weteor/Fitis/pcb/fitis.kicad_sch

## KiCad design pcb/fitis.kicad_sch (2024-07-09)

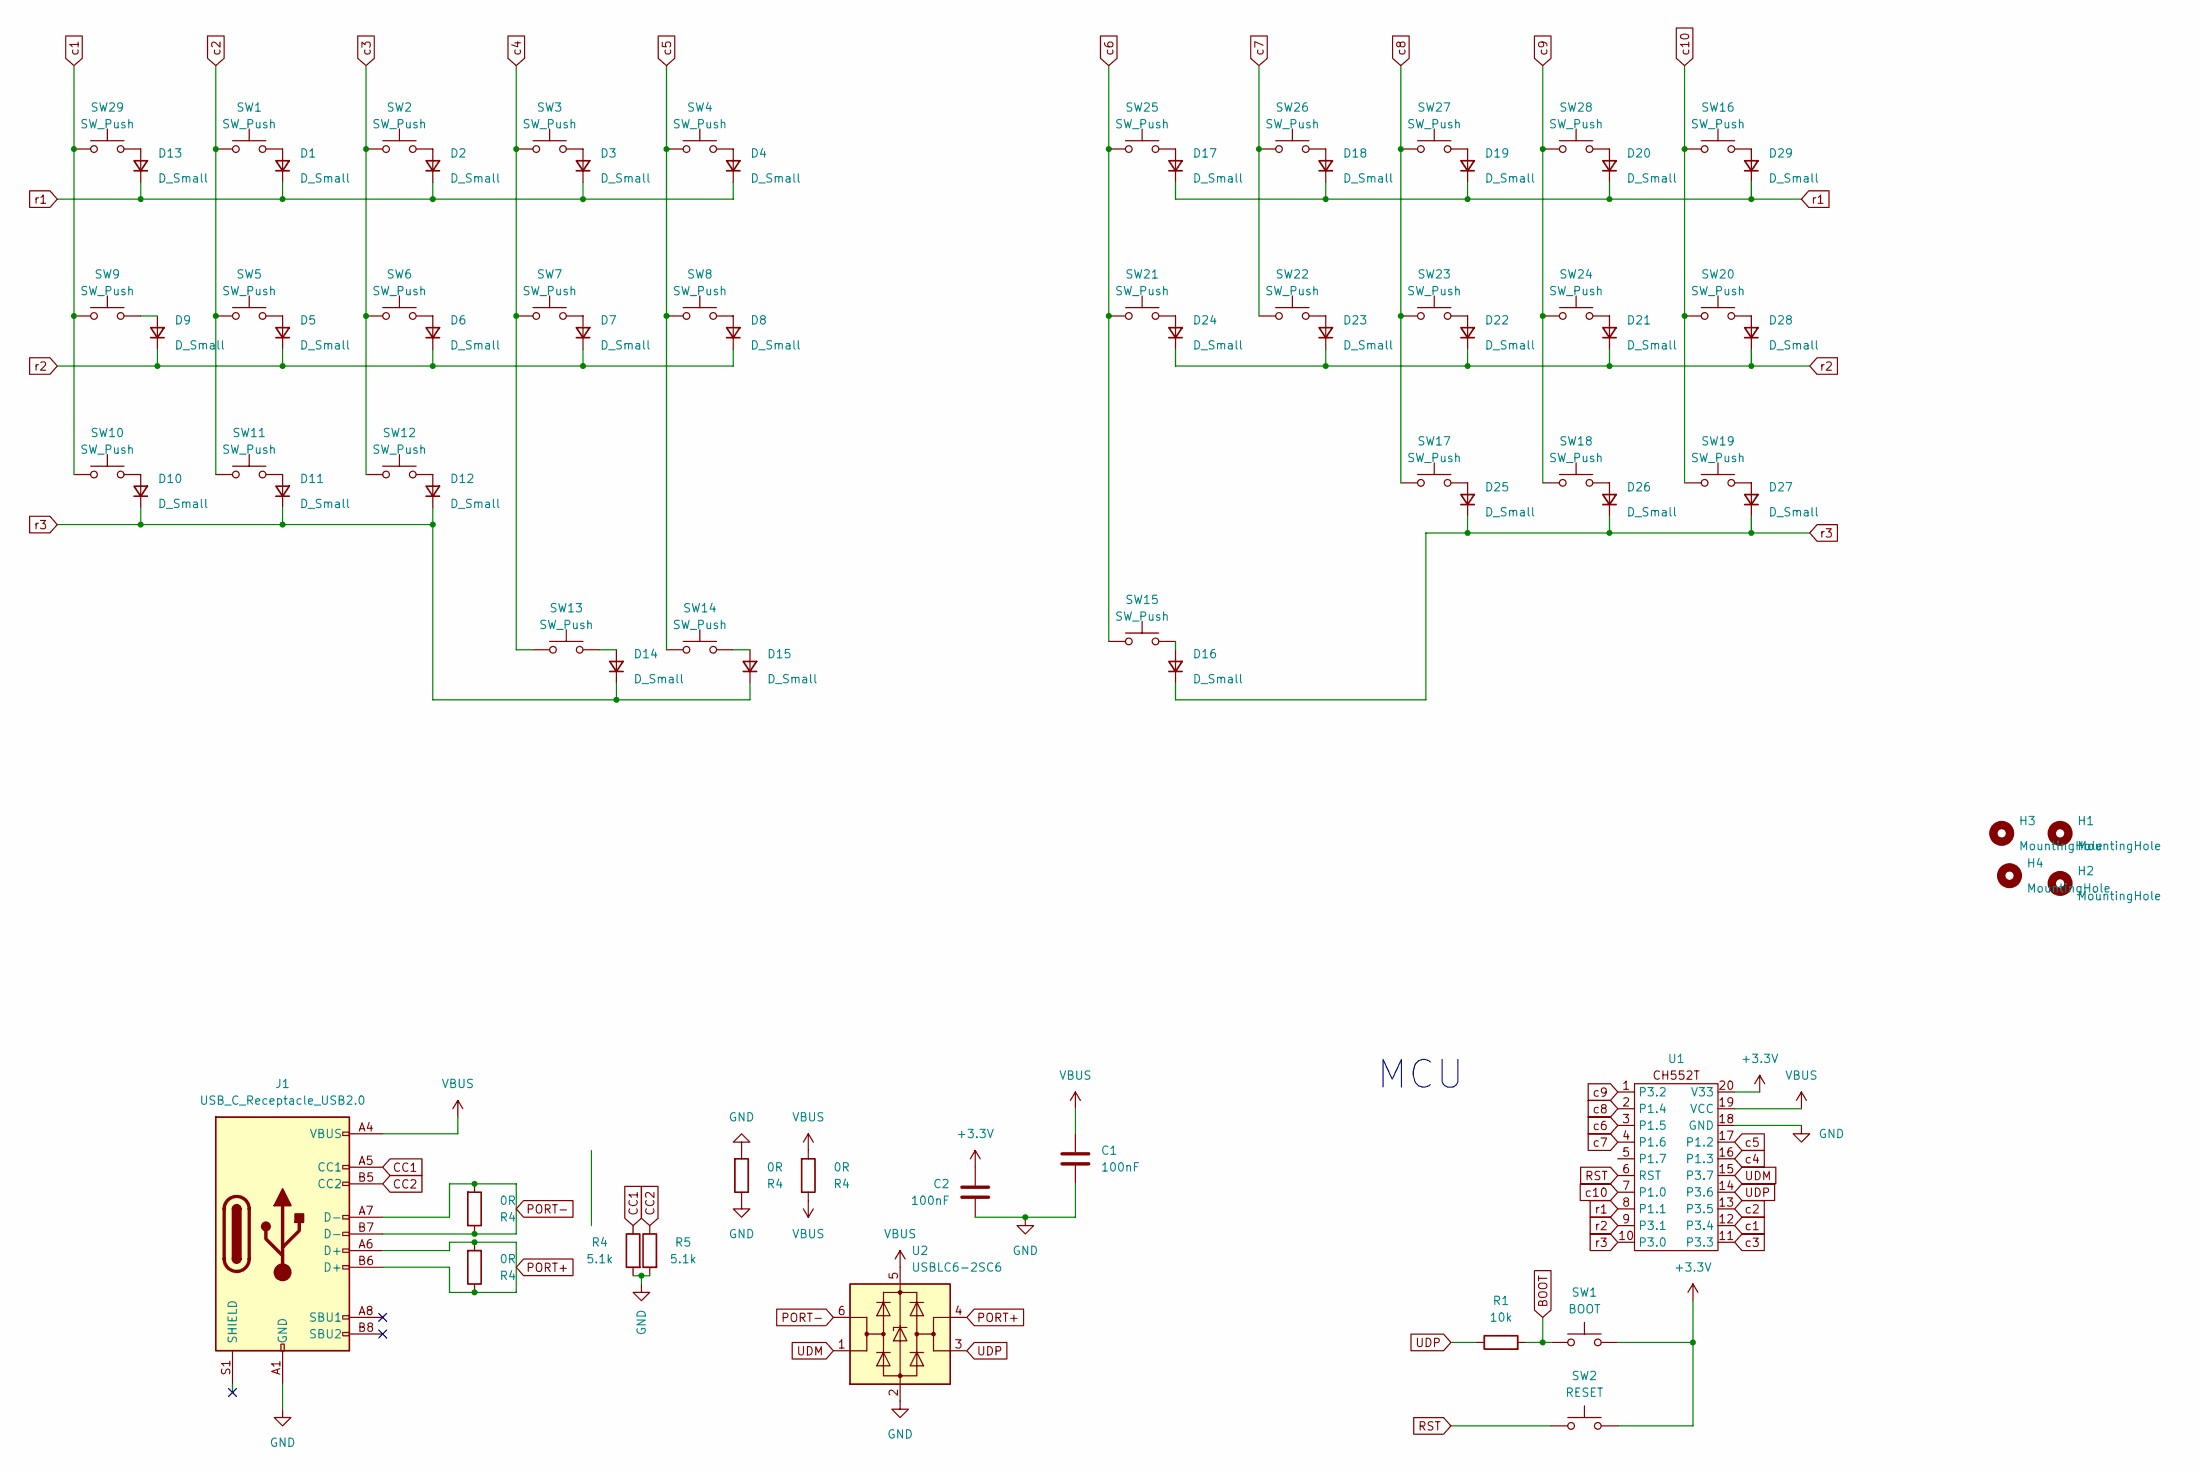
[picture p4: schematic fitis.kicad_sch]

Parts:
C1, C2: 100nF; C_0603_HandSolder; LCSC C1525
D1, D2, D3, D4, D5, D6, D7, D8, D9, D10, D11, D12, D13, D14, D15, D16, D17, D18, D19, D20, D21, D22, D23, D24, D25, D26, D27, D28, D29: D_Small; D_SOD-123
H1, H2, H3, H4: MountingHole; MountingHole_2.2mm_M2
J1: USB_C_Receptacle_USB2.0; USB-C-12-Pin-MidMount
R1: 10k; R_0603_HandSolder; LCSC C25744
R4: 0R; R_0603_HandSolder
R5: 5.1k; R_0603_HandSolder
SW1: BOOT; SW_SPST_TL3342; LCSC C115357
SW2: RESET; SW_SPST_TL3342; LCSC C115357
SW3, SW4, SW5, SW6, SW7, SW8, SW9, SW10, SW11, SW12, SW13, SW14, SW16, SW17, SW18, SW19, SW20, SW21, SW22, SW23, SW24, SW25, SW26, SW27, SW28, SW29: SW_Push; ChocV1_V2_Hotswap_3d
SW15: SW_Push; ChocV1_V2_Hotswap_1.5u_3d
U1: TSSOP-20_4.4x6.5mm_P0.65mm; JLCPCB_CORRECTION 0; 0; 270
U2: USBLC6-2SC6; SOT-23-6; JLCPCB_CORRECTION 0; 0; 270

Connections:
+3.3V: C2.1, SW1.2, SW2.2, U1.20 (V33)
BOOT: R1.2, SW1.1
CC1: J1.A5 (CC1), R4.1
CC2: J1.B5 (CC2), R5.1
GND: C1.2, C2.2, J1.A1 (GND), J1.A12 (GND), J1.B1 (GND), J1.B12 (GND), R4.1, R4.2, R5.2, U1.18 (GND), U2.2 (GND)
unnamed: D1.2 (A), SW1.2
unnamed: D2.2 (A), SW2.2
unnamed: D3.2 (A), SW3.2
unnamed: D4.2 (A), SW4.2
unnamed: D5.2 (A), SW5.2
unnamed: D6.2 (A), SW6.2
unnamed: D7.2 (A), SW7.2
unnamed: D8.2 (A), SW8.2
unnamed: D9.2 (A), SW9.2
unnamed: D10.2 (A), SW10.2
unnamed: D11.2 (A), SW11.2
unnamed: D12.2 (A), SW12.2
unnamed: D13.2 (A), SW29.2
unnamed: D14.2 (A), SW13.2
unnamed: D15.2 (A), SW14.2
unnamed: D16.2 (A), SW15.2
unnamed: D17.2 (A), SW25.2
unnamed: D18.2 (A), SW26.2
unnamed: D19.2 (A), SW27.2
unnamed: D20.2 (A), SW28.2
unnamed: D21.2 (A), SW24.2
unnamed: D22.2 (A), SW23.2
unnamed: D23.2 (A), SW22.2
unnamed: D24.2 (A), SW21.2
unnamed: D25.2 (A), SW17.2
unnamed: D26.2 (A), SW18.2
unnamed: D27.2 (A), SW19.2
unnamed: D28.2 (A), SW20.2
unnamed: D29.2 (A), SW16.2
PORT+: J1.A6 (D+), J1.B6 (D+), R4.1, R4.2, U2.4 (I/O2)
PORT-: J1.A7 (D-), J1.B7 (D-), R4.1, R4.2, U2.6 (I/O1)
RST: SW2.1, U1.6 (RST)
UDM: U1.15 (P3.7), U2.1 (I/O1)
UDP: R1.1, U1.14 (P3.6), U2.3 (I/O2)
VBUS: C1.1, J1.A4 (VBUS), J1.A9 (VBUS), J1.B4 (VBUS), J1.B9 (VBUS), R4.1, R4.2, U1.19 (VCC), U2.5 (VBUS)
c1: SW9.1, SW10.1, SW29.1, U1.12 (P3.4)
c2: SW1.1, SW5.1, SW11.1, U1.13 (P3.5)
c3: SW2.1, SW6.1, SW12.1, U1.11 (P3.3)
c4: SW3.1, SW7.1, SW13.1, U1.16 (P1.3)
c5: SW4.1, SW8.1, SW14.1, U1.17 (P1.2)
c6: SW15.1, SW21.1, SW25.1, U1.3 (P1.5)
c7: SW22.1, SW26.1, U1.4 (P1.6)
c8: SW17.1, SW23.1, SW27.1, U1.2 (P1.4)
c9: SW18.1, SW24.1, SW28.1, U1.1 (P3.2)
c10: SW16.1, SW19.1, SW20.1, U1.7 (P1.0)
r1: D1.1 (K), D2.1 (K), D3.1 (K), D4.1 (K), D13.1 (K), D17.1 (K), D18.1 (K), D19.1 (K), D20.1 (K), D29.1 (K), U1.8 (P1.1)
r2: D5.1 (K), D6.1 (K), D7.1 (K), D8.1 (K), D9.1 (K), D21.1 (K), D22.1 (K), D23.1 (K), D24.1 (K), D28.1 (K), U1.9 (P3.1)
r3: D10.1 (K), D11.1 (K), D12.1 (K), D14.1 (K), D15.1 (K), D16.1 (K), D25.1 (K), D26.1 (K), D27.1 (K), U1.10 (P3.0)

Notes on the sheet:
MCU
